mferris/FlightRadar/HANDOFF.md

# FlightRadar — Handoff Notes

## Status
`index.html` is a matured version of `docs/original-prototype.html` that renders
**live** aircraft on the round radar instead of the fake demo data. It has been
tested against the real receiver at `http://192.168.4.77/tar1090/` and confirmed
working: live positions, altitude-coded colors, smooth interpolation between
1s polls, a "NO SIGNAL" banner on connection loss (tested by killing the feed),
and clean recovery on reconnect.

It is now **deployed and running on the Pi** (`[hostname-redacted]`, `192.168.4.77`,
user `mferris`) as a Chromium kiosk launched by systemd, verified to survive a
full reboot with no manual intervention.

**Naming note**: the project was renamed FlightWall → FlightRadar -- repo,
app title, bundle ID, deploy service/file names, and the live services
actually running on the Pi are all updated (`flightradar-kiosk.service`,
`flightradar-photo-proxy.service`, `flightradar-approach-store.service`,
`/opt/flightradar/`, lighttpd confs `89`/`91-flightradar-*.conf`). The
approach-track store's accumulated data (4,788 points at migration time)
was preserved across the cutover: fetched via the old service's own GET
`/approaches` before touching anything, POSTed into the new service after
it was up, verified the count matched on both sides before deleting the
old service/files. The **Pi's actual system hostname is still
`[hostname-redacted]`**, and the Tailscale Funnel URL is unchanged too — those are
real infrastructure identifiers, not just branding, and changing them would
mean re-registering Tailscale and likely getting a new Funnel URL (breaking
any existing bookmarks/links). Left alone deliberately; revisit only if
that's ever specifically wanted. (The real hostname itself, along with the
receiver's exact address/coordinates, is intentionally kept out of this
repo -- see the "Security & going public" section below. The iOS app's
`APIConfig.defaultBaseURL` now defaults to the generic `raspberrypi.local`
instead, with your own real hostname set locally in Settings.)

## Display center override
`index.html` has a `HOME_OVERRIDE` constant that, when set, centers the
radar/map/runway lookup on a fixed point instead of the receiver's real
position — deliberately **display-only**, never touching `readsb`'s actual
configured position (`/etc/default/readsb`, `--lat`/`--lon`), which needs to
stay accurate to the real antenna for its own signal-range/MLAT math.

**Currently `null`** — back to auto-detecting the real receiver position
from `receiver.json` (confirmed against the real antenna's configured
`--lat`/`--lon` to within normal geocoding precision). It was briefly set to
a different address for a one-off request, then reverted.

If it's ever set again: `loadHome()` skips fetching `receiver.json` and uses
the override synchronously instead, and `normalizeAircraft()` always
computes bearing/range via haversine from raw lat/lon rather than trusting
readsb's precomputed `r_dst`/`r_dir` — those are relative to the *real*
antenna position, not an override point, and would silently produce a
geometrically-inconsistent display if trusted while overridden. (Verified by
hand while it was active: an aircraft readsb reported `r_dst: 3.77` for
showed up correctly as `14.53` in FlightRadar — its true haversine range from
the override point.) Also worth knowing: a override point far from the real
antenna shifts the visible 40nm disc so it only partially overlaps the
antenna's actual reception area.

## Remote access (Tailscale Funnel)
The page is also reachable from outside the local network via Tailscale
Funnel, at the same real hostname noted above (kept out of this repo) —
publicly
reachable HTTPS, no login/app required for whoever you send the link to, no
router port-forwarding involved. `tailscale` is installed on the Pi, signed
into `mferris`'s tailnet, with `tailscale funnel --bg 80` proxying that
public URL to lighttpd on `127.0.0.1:80` (the same server `index.html` and
`/tar1090/` are already deployed to, so this is the exact same page, not a
separate copy). Funnel exposes the **whole** site, not just `index.html` —
`/tar1090/` itself is also reachable at that URL, fine for this use case
since it's just flight data, but worth remembering before deploying anything
more sensitive to this docroot later.
- Check status: `ssh mferris@192.168.4.77 tailscale funnel status`
- Turn off: `ssh mferris@192.168.4.77 sudo tailscale funnel --https=443 off`
- The Funnel/serve config is stored in tailscaled's persistent state, so it
  should come back automatically on reboot (not yet verified with an actual
  reboot test the way the kiosk service was — worth confirming if this
  matters going forward).

### Hardening done after enabling Funnel
Turning Funnel on prompted a quick look at what else was reachable on the
Pi. Two things worth knowing:
- **readsb's raw/Beast/SBS ports (30001-30005, 30104) are now bound to
  `127.0.0.1` only** (`--net-bind-address 127.0.0.1` added to `NET_OPTIONS`
  in `/etc/default/readsb`, original backed up alongside as
  `readsb.bak`). They used to listen on `0.0.0.0` — reachable from the whole
  LAN — but nothing on the network was actually connected to them, and
  FlightRadar/tar1090 don't use them at all (they read the JSON files readsb
  writes to disk, not these TCP ports). If you ever want to feed a live raw
  feed to another device on your LAN (Virtual Radar Server, a second
  receiver dashboard, etc.), you'll need to revert this
  (`sudo cp /etc/default/readsb.bak /etc/default/readsb && sudo systemctl
  restart readsb`).
- **Deliberately left `mferris`'s passwordless sudo as-is.** Requiring a
  password would block the non-interactive SSH commands this whole project's
  deployment workflow depends on. This is a real trade-off, not an
  oversight — revisit if that workflow ever changes (e.g. moving deploys to
  a proper CI pipeline instead of ad-hoc SSH).
- **Network segmentation (Eero guest network) was suggested but not done**
  — the Pi's on `wlan0` (WiFi, not Ethernet), so Eero's guest network
  feature would apply cleanly, but doing this yourself: it isolates the Pi
  from the rest of the LAN, which also means your other devices lose
  ad-hoc local access to `http://192.168.4.77/` — Tailscale (already set up
  for Funnel) would keep working as the way to reach the Pi afterward,
  network-topology-independent.

The radar also now has a **background map** (MapLibre GL JS, vendored under
`vendor/` — BSD-3-Clause, v5.24.0, self-hosted so the only runtime network
dependency is the tile/style fetch itself). The map is non-interactive
(`interactive: false`), centered on `home`, and zoomed so its visible extent
matches the radar's `RANGE_NM` ring exactly (`zoomForRange()` in
`index.html` derives the zoom level from the standard Web Mercator
meters-per-pixel formula — recomputes correctly if `RANGE_NM` or the
receiver location ever changes, nothing hardcoded). Requires the Pi to have
internet access for tiles (confirmed working); the ADS-B tracking itself has
no such dependency and keeps working if the map layer fails to load (falls
back to the original solid dark background via CSS).

**Style is OpenFreeMap's `liberty`**, not their `dark` style — `dark` turned
out to be near-grayscale by design (checked the actual style JSON: water,
parks, and woods are all defined at ~0% saturation), so no amount of CSS
`saturate()` could pull color out of it. `liberty` has real color (blue
water, green parks, warm orange/yellow road tones) which we darken ourselves
via `#mapbg`'s CSS `filter: brightness(0.3) saturate(1.5)` — tuned live in a
few iterations to land on "still reads as a dark backdrop" without going all
the way back to washed-out or invisible. Since `liberty` is styled for a
light background (place-name labels are black text with a white halo),
`recolorLabels()` flips city/town/village/water-name labels to light
text/dark halo after the style loads, via the same `setPaintProperty`
pattern already used for the runway layer colors — otherwise the labels
would darken along with everything else and become illegible.

The map also shows **real runway outlines** at airports in range (e.g. RDU's
crossing-runway pattern). The OpenFreeMap tileset's own `aeroway-*` layers
turned out to be a dead end — confirmed via `queryRenderedFeatures()` that the
vector tiles simply carry no runway/taxiway geometry below zoom ~11, and our
fixed radar zoom is ~9.7, so raising the style's `minzoom` did nothing (the
data isn't in the tile, not just hidden). Runways instead come from a
one-time query to OSM's public Overpass API (`loadRunways()`, fired once from
`map.on('load', ...)` since the receiver's home location never changes at
runtime), added as our own GeoJSON source/layers — this bypasses the vector
tileset's zoom restriction entirely since a GeoJSON source isn't tile-paginated.
Purely additive: if Overpass is unreachable the map/radar work exactly as
before, just without runway outlines.

Each tracked aircraft now shows a **color-coded airline badge** (full name,
e.g. "Piedmont Airlines" — or "Private Aircraft" for GA/unidentified flights),
a **human-readable aircraft type** (e.g. "Bombardier Regional Jet CRJ-900",
"Bell 429 GlobalRanger"), and its **route** as city names (e.g. "Tampa →
London") when one's known. A few deliberate choices here, worth preserving:
- **No real airline logos.** They're trademarked, and this project is meant
  to be published under MIT — bundling them would ship trademarked assets in
  an openly-redistributable repo. The `AIRLINES` table in `index.html` instead
  has a small hand-picked set of ICAO designators (ICAO Doc 8585, a public
  standard) mapped to a full name/IATA code/loosely-associated color, rendered
  as a generated text badge. Not exhaustive — unmapped carriers just fall
  back to the airline's ICAO code not being in the table (rare); anything
  whose callsign doesn't match the airline-flight-number pattern at all
  (`/^[A-Z]{3}\d/`) gets "Private Aircraft" instead.
- **Route data comes from `https://adsb.im/api/0/routeset`** — the same free,
  no-key API `tar1090` itself already uses on this Pi (confirmed by reading
  `planeObject_*.js`'s `routeDoLookup()` on the box). ADS-B itself carries no
  route info at all. Lookups are batched/cached/throttled in `index.html`
  (`queueRouteLookup`/`flushRouteQueue`) the same way tar1090 does it: one
  POST per `ROUTE_BATCH_MS` (4s), results cached for the rest of the session
  (including negative "no route found" results, so unknown callsigns aren't
  re-queried every cycle). Routes the API itself flags `plausible: false` are
  treated as unknown rather than displayed (tar1090 doesn't bother with this
  check, but showing a route the API itself doubts felt worse than omitting
  it). Displays city names (`_airports[].location`) rather than IATA codes.
- **Aircraft type also has no field in `aircraft.json`** — readsb doesn't
  populate `t`/`desc` there. tar1090 solves this the same way it solves
  routes: a local same-origin database, this time already sitting on the Pi
  as a prefix-trie of small JSON shards under `/tar1090/db-<hash>/` (the hash
  changes whenever tar1090's assets rebuild, so `index.html` discovers the
  current folder name at runtime by regexing it out of `/tar1090/index.html`
  rather than hardcoding it — see `discoverDatabaseFolder()`). `lookupType()`
  walks that trie itself (own implementation, not copied — tar1090's own code
  license is unclear ["Other"/NOASSERTION on GitHub], so this reads the same
  public same-origin data files but isn't a port of their `dbloader.js`).
  Falls back to `icao_aircraft_types2.js` (ICAO type-code -> description) when
  a specific tail's entry has no `typeLong` of its own. `humanizeType()` just
  re-cases ALL-CAPS manufacturer names ("CIRRUS SR-22" -> "Cirrus SR-22")
  without touching model numbers.

**Labels live in a ring around the edge of the dial**, not floating next to
their plane — each label's natural position is its own bearing angle
(`LABEL_RING_RADIUS = R + 60`), eased there via `LABEL_SPRING_TAU` as the
plane moves, and a color-matched SVG leader line (`#leaders`) always
connects the label back to its actual plane position (attached to whichever
edge of the box faces the plane, via `closestPointOnRect()`). Overlap
resolution (`LABEL_SEPARATION_PASSES` iterations) only ever adjusts a
label's *angle* along the ring, never pulls it off — and always resolves
bearing-adjacent neighbors in bearing-sorted cyclic order. That order
preservation is what guarantees leader lines never cross (a standard
property: connecting points on an inner circle to points on an outer ring
in the same cyclic order can't produce crossing chords), not just an
approximation of "minimized." `R` was shrunk from `0.44*W` to `0.38*W` to
free up a real outer band for the ring to live in. One known rough edge:
a label very close to due-north bearing can lightly touch the HUD text at
the top of the stage — rare, and it's a HUD/label interaction rather than
label-on-label overlap, but not yet fixed. This replaced an earlier
version that eased each label toward a fixed offset next to its plane with
plain 2D AABB separation — that avoided label-on-label overlap fine but had
no concept of leader-line crossings at all.

Covers milestones 3–6 and part of 7 from `docs/project-spec.md` — **the round
panel is physically connected now** (HDMI + USB-C touch + its own 5V power via
a USB-C PD charger, confirmed working: `xrandr` shows `HDMI-A-1 connected
1080x1080`, touch enumerates as `Waveshare Waveshare-079-HD` at USB ID
`0712:000a`), and milestone 5 (tap detail panel) is done too. Backlight
brightness has a physical button on the driver board (per Waveshare's docs,
it also supports "HID software dimming" but no public documentation of that
protocol was findable — button is the practical path for now). Not done:
physically mounting the finished enclosure (that's fabrication, not
software).

## Touch interaction (milestone 5)
Tap a plane's blip or label → detail panel (registration, heading, vertical
rate, squawk, precise range/bearing, and now a real photo — see below). Tap
empty space → cycles three display modes (full / map off / map+labels off)
with a toast confirming the mode. Hit-testing is manual coordinate math on
one delegated `pointerup` listener on `.stage`, not per-element
`pointer-events` (the tag divs are `pointer-events:none` by design, and
label positions move every frame anyway). See `findPlaneAtStagePoint()` —
worth knowing: it returns the *first* match in `planes` iteration order, not
the *nearest*, so two blips/labels overlapping within the ~22px hit radius
could occasionally resolve to the "wrong" one of the two. Not fixed, low
stakes (tapping again elsewhere and retrying works fine).

**Aircraft photo**: `deploy/photo-proxy.py` is a small local-only (127.0.0.1)
Python service on the Pi, proxying planespotters.net's photo API — their API
requires a descriptive custom `User-Agent` naming the app, which browser
`fetch()` can never set itself (browsers own that header exclusively), so
this has to happen server-side. `deploy/89-flightradar-photo-proxy.conf`
(lighttpd, `mod_proxy`) routes `/photo/<hex>` to it so the browser's fetch
stays same-origin. Runs as `flightradar-photo-proxy.service`
(`DynamicUser=yes`, no privileges needed), in-memory cache per hex, 24h TTL.
Attribution (required by planespotters.net's terms — photographer credit +
naming the source) is shown as **plain non-clickable text**, not a real
`<a>` link — deliberate, since this same `index.html` also runs unattended
in the kiosk's own Chromium, and risking a tap navigating the kiosk away
from the app with no way back wasn't acceptable, even though a real link
would be fine in a normal browser tab (e.g. via the Funnel URL). Gracefully
shows nothing if planespotters has no photo for that airframe.

## Key facts learned this session
- Receiver home location comes from `http://192.168.4.77/tar1090/data/receiver.json`
  (`lat`/`lon`) — the app fetches this itself at startup rather than hardcoding it.
  Currently somewhere in the Raleigh-Durham area (exact coordinates intentionally
  not recorded here — see "Security & going public" below).
- `aircraft.json` entries already include `r_dst` (range, nm) and `r_dir` (bearing,
  deg) precomputed by readsb relative to the receiver — `index.html` uses these
  directly and only falls back to a haversine calc from raw `lat`/`lon` if they're
  ever missing.
- The Pi's web server (lighttpd) does **not** send CORS headers, so `index.html`
  must be deployed same-origin (i.e. copied onto the Pi itself, served from the
  same host as `/tar1090/`) — it uses relative fetch paths (`/tar1090/data/...`)
  for exactly this reason.
- SSH login is `mferris@192.168.4.77` (not `pi` — that user doesn't exist on this
  image). Passwordless sudo is configured for `mferris`.
- The Pi runs full Raspberry Pi OS (Debian 13 "trixie") with a Wayland desktop
  (`labwc` compositor, `rpd-labwc` session), lightdm with autologin already
  configured for `mferris`. Not a Lite/headless image.
- The round display was **not physically connected** during this session (both
  HDMI ports read `disconnected` via `/sys/class/drm/*/status`) — the compositor
  falls back to a virtual/no-op 1920x1080 output. Everything was verified via
  `grim` screenshots of that virtual output; the app has not yet been visually
  confirmed on the real 1080x1080 round panel.

## Deployment (milestone 6 — done)
- `index.html` lives at `/var/www/html/index.html` on the Pi (root-owned,
  lighttpd's docroot), served at `http://localhost/` — same-origin with
  `/tar1090/`, satisfying the CORS constraint above.
- Kiosk launcher is a **systemd user service**, checked into this repo at
  `deploy/flightradar-kiosk.service` and deployed to
  `~/.config/systemd/user/flightradar-kiosk.service` on the Pi (as `mferris`).
  - Launches `chromium --kiosk ... http://localhost/index.html`
  - `ExecStartPre` waits (up to 60s) for a `wayland-*` socket in
    `$XDG_RUNTIME_DIR` before starting Chromium — needed because the compositor
    isn't up yet at the instant lightdm opens the session. **Important:** don't
    wait on the `$WAYLAND_DISPLAY` env var itself (e.g.
    `-S "$XDG_RUNTIME_DIR/$WAYLAND_DISPLAY"`) — that variable is imported into
    the systemd user manager *after* labwc starts, so a process forked right at
    session-open captures it empty and waits forever. Glob for `wayland-*[0-9]`
    instead.
  - `Restart=always`, `RestartSec=5` for crash recovery.
  - Enabled via `systemctl --user enable` (symlinked into
    `default.target.wants`), plus `sudo loginctl enable-linger mferris` so the
    user's systemd instance starts at boot even before an interactive login
    completes.
- Verified with an actual `sudo reboot`: service came up ~30s after boot with
  zero restarts, no manual login needed, and was rendering live traffic.
- To redeploy `index.html` after future edits:
  `scp index.html mferris@192.168.4.77:/tmp/ && ssh mferris@192.168.4.77 'sudo cp /tmp/index.html /var/www/html/index.html && rm /tmp/index.html'`
  (Chromium will pick it up on next reload/kiosk restart — no service restart
  needed unless the launch flags/URL change.)

## Approach-track store moved from localStorage to a shared server-side service
The RDU approach-track heatmap (below) originally persisted to
`localStorage` — turns out that's scoped per-browser/per-device, so the
kiosk's own accumulated picture was never visible to anyone checking the
page from a separate browser (laptop, phone, the Funnel URL) — each one
just sees its own empty history. Moved to a small same-origin service
instead, same shape as `deploy/photo-proxy.py`:

- **`deploy/approach-store.py`** — a tiny stdlib-only HTTP server on
  `127.0.0.1:8082`. `GET /approaches` returns the accumulated points (JSON
  array of `[lon, lat]`); `POST /approaches` appends more, capped at
  `MAX_POINTS = 6000` (oldest evicted first — the client-side cap in
  `index.html` is now just a courtesy against pathological cases; the
  server enforces its own copy of the same limit regardless). No auth, no
  dedup — multiple viewers open at once could each independently report
  the same real landing, which just over-represents that landing by a
  point or two, not a correctness problem worth the complexity of fixing.
- **`deploy/91-flightradar-approach-store.conf`** (lighttpd, `mod_proxy`)
  routes `/approaches` to it, keeping the browser's `fetch()` same-origin —
  same pattern as `89-flightradar-photo-proxy.conf`.
- **`deploy/flightradar-approach-store.service`** — `DynamicUser=yes`,
  `NoNewPrivileges=yes`, matching `flightradar-photo-proxy.service`, plus
  `StateDirectory=flightradar-approaches` so `approaches.json` survives
  restarts/reboots despite the dynamic user (systemd creates/owns
  `/var/lib/flightradar-approaches` and hands the path to the service via
  `$STATE_DIRECTORY`).
- `index.html`: `loadApproachPoints()` (GET, fired non-blocking at startup
  alongside the type-database discovery) replaces the old synchronous
  `localStorage.getItem` read; `commitApproachTrack()` now updates the
  local in-memory view immediately (so *this* session's map stays
  responsive) and separately fire-and-forgets a POST so the commit is
  shared with everyone else, current and future.

Verified the whole chain locally: GET/POST/cap/eviction behavior on the
service directly, persistence across a service restart, and — the actual
point of this change — that a second, completely independent browser tab
loading the page sees the exact points a first tab had just committed,
proving the "shared across viewers" behavior actually works and isn't just
each browser talking to itself. Deployed and confirmed no regression to the
sibling `tar1090`/`photo-proxy` endpoints already served through lighttpd.

## RDU approach-path visualization (two complementary pieces)
Requested: faint outlines of RDU's approach paths. No good free dataset of
*real* approach procedures exists (unlike runways, which OSM/Overpass has
real geometry for -- FAA approach plates are PDF charts, not simple line
data), so this ended up as two complementary pieces:

1. **`extendedApproachLines()`** (in `loadRunways()`) -- an immediate,
   free approximation: extends each real runway's own centerline outward
   (`RUNWAY_EXTENSION_NM = 8`, roughly a typical ILS/RNAV final segment
   length) using a new `destinationPoint()` helper (the geodesic inverse of
   `haversineBearingRange()` -- given a start point + bearing + distance,
   find the destination). Real final approaches always align with the
   runway heading for the last several miles regardless of which specific
   procedure guides them there, so this is a reasonable stand-in with zero
   new data dependency. Styled faint/dashed (`line-opacity: 0.22`,
   `line-dasharray`) and added to the map *before* the real runway/taxiway
   layers so the crisp real pavement paints on top of it, not competing.

2. **Real accumulated approach tracks** (`updateApproachTracking()`,
   `confirmApproachOnDrop()`, `commitApproachTrack()`) -- the more
   interesting piece: builds a picture from aircraft *actually observed*
   landing at RDU, growing more defined the more landings it sees.
   Candidate points get buffered per-plane (`pl.approachPoints`) while a
   plane is within `RDU_APPROACH_RADIUS_NM` (12) and below
   `RDU_APPROACH_CEILING_FT` (field elevation + 6000ft) -- deliberately
   loose criteria, since bad data is filtered at *confirmation*, not
   collection. A buffer only gets committed to the persistent store if the
   plane is later confirmed to have actually landed: either it reaches
   `'ground'` status within `RDU_APPROACH_CONFIRM_RADIUS_NM` (2.5nm), or --
   since ADS-B reception commonly drops out right at touchdown, especially
   before a receiving antenna is mast-mounted -- it disappears (coasts out
   past `COAST_TOTAL_MS`) close to the field at low altitude
   (`RDU_APPROACH_CONFIRM_ALT_FT`, field elevation + 1500ft). If instead a
   plane climbs back out or flies away without either signal, its buffer is
   discarded -- overflights and go-arounds don't shape the picture, only
   real landings do. Verified all of this directly (buffered-then-committed,
   buffered-then-discarded-on-go-around, and the signal-loss-near-ground
   path) by driving the functions with synthetic lat/lon/alt sequences.

   Persisted to `localStorage` (`flightwall_rdu_approaches_v1`, capped at
   `APPROACH_MAX_POINTS = 6000`, oldest evicted first) so it keeps building
   across kiosk reboots/reloads, not just within one session -- confirmed
   this survives an actual page reload. Rendered as a MapLibre `heatmap`
   layer (`approaches-heat`), tuned low-intensity/faint on purpose, added
   at `map.on('load', ...)` time alongside `loadRunways`/`recolorLabels`/
   `refreshStorms` -- since it has no network dependency (just reads
   localStorage), it always finishes before `loadRunways`'s Overpass
   round-trip does, so the real runway lines naturally paint on top of it
   without needing explicit layer ordering.

   Starts empty on a fresh install by design -- there's no way to
   backfill history, only real traffic from here forward builds it up.

**Testing note**: hit real trouble getting a clean live screenshot of this
in the sandbox's browser preview this session -- MapLibre's `'load'` event
never fired no matter what (confirmed via a throwaway map instance with a
hardcoded zoom, ruling out anything in our own code; also confirmed
OpenFreeMap's style endpoint itself was reachable and fast). Looked like a
stuck WebGL/rendering-context issue specific to that browser-pane process,
possibly from creating many map instances across today's testing without
disposing them -- survived closing tabs and even a full preview-process
restart, so treat it as a known rough edge of long testing sessions in that
environment, not a real bug. Fell back to verifying via direct function
calls (thorough) and a real `grim` screenshot of the actual kiosk (confirmed
the map/runway rendering pipeline itself is unaffected and healthy).

**Unrelated but important, found while checking the kiosk**: the round
panel's physical HDMI connection was down at the time
(`/sys/class/drm/card1-HDMI-A-1/status: disconnected`, compositor fell back
to its virtual/no-op output, same as before the panel was ever connected)
-- a hardware/cable issue, not caused by this deploy. Worth a physical check
next time someone's at the Pi, especially since the new FlightAware antenna
was recently connected and cables may have been disturbed.

## Stock photo hit rate was much lower than it should've been
Reported as "a lot of planes, especially private ones, can tell me the type
but can't find a stock picture." Two real bugs, both in `lookupStockPhoto()`:

1. Was using `action=opensearch`, which only **prefix**-matches Wikipedia
   page *titles* — a much narrower match than it looks like at a glance.
   `typeLabel` strings like "Bombardier Regional Jet CRJ-900" don't share a
   leading prefix with Wikipedia's actual title ("Bombardier CRJ"), so
   opensearch came back empty even though a perfectly good article and photo
   exist. Switched to `action=query&list=search` (real full-text search over
   article content, word order doesn't matter) — confirmed via a real
   browser `fetch()`, not `curl` (see below for why that distinction
   mattered), that this resolves cases opensearch couldn't.
2. **The bigger one**: any failed lookup — including a purely transient one,
   like a momentary network hiccup or rate-limit — was being cached as a
   permanent `null`. Once a given aircraft *type* failed once, it would
   never show a photo again for the rest of the session, no matter how many
   different tails of that type got tapped afterward. This is the exact same
   failure shape `loadRunways()` had before its retry fix, just showing up
   as "this type never gets a photo" instead of "runways never load."
   Fixed by only caching *successful* lookups — a failed one just retries
   next time that type's panel is opened, which is cheap and naturally
   bounded by tap frequency (same tradeoff the specific-tail planespotters
   photo lookup already makes: it isn't cached at all, and re-fetches every
   single time a panel opens).

Worth knowing for next time: while testing, `curl`-hammering Wikipedia's API
rapidly with no descriptive User-Agent tripped an actual 429 ("Please set a
proper user-agent and respect our robot policy") from their edge cache.
That's a `curl`-testing artifact, not something the real app should hit —
browser `fetch()` always sends a real browser UA, and lookups only ever fire
on a human tap, nowhere near hammering pace — but it's worth remembering if
Wikipedia lookups ever look flaky again: check whether it's a real app-level
issue before assuming it's the app doing something wrong, since aggressive
manual testing against the same API can produce misleading transient
failures that don't reflect real usage.

## Runways silently disappearing for a whole session (found this session)
Reported as "I can no longer see the RDU runways." Root cause turned out to
be unrelated to the map alignment fix above — a real, separate,
pre-existing gap: `loadRunways()` only ever ran **once**, on the map's
`load` event, with no retry. A single transient failure from Overpass
(rate-limited, timed out, etc.) at exactly the wrong moment — like right as
the kiosk boots — silently and *permanently* lost runways for that entire
session, since nothing else ever re-triggered the fetch and the kiosk can
run for days before its next reload. Confirmed by hand: called
`loadRunways()` directly a few times back-to-back while testing (which
itself hammers the same shared public Overpass instance) and watched it
return with zero features/an error a couple of times before a retry
succeeded with real data — the exact failure mode, reproduced live. Likely
tripped for real this session specifically because the kiosk got restarted
six separate times deploying today's other changes, each one a fresh
chance to hit it.

Fixed with a bounded retry: up to `OVERPASS_MAX_ATTEMPTS` (4) tries, 20s
apart (`OVERPASS_RETRY_MS`) — generous backoff since this is a shared public
API and only needs to eventually land once per (rare) kiosk reload, not be
fast. Still purely additive/best-effort after retries are exhausted, same as
before — the map/radar work fine without runway outlines either way.

## Trails made always-on for every plane, not just tap-to-show
Preference change: flight trails (see below) now draw for every in-range
aircraft every frame (`drawTrails()`), not just the one with an open detail
panel. The trail *data* was already being collected for every plane
regardless of selection (that was deliberate from the start, so reopening a
panel would show continuity) — only the drawing itself was gated.

Also shortened `TRAIL_MAX_MS` from 10 minutes to 3. That was sized for "one
plane, deep history, only while you're looking at it" — rendering it for
every plane simultaneously, permanently (not just while a panel happens to
be open), is a meaningfully bigger continuous per-frame cost on a Pi running
this render loop 24/7 (up to ~600 line segments per aircraft at the old
window, times however many are in view at once), and a 10-minute trail per
plane all at once is also visually noisy. 3 minutes still clearly shows an
approach/departure into RDU. Worth revisiting (either direction) once seen
running for a while on the real hardware.

## Stock photo fallback for tails with no planespotters photo
Most tracked tails (private/GA especially) have no dedicated planespotters
photo — noticed by actually clicking around on GA traffic. Rather than
always falling back to the generic silhouette, `tryStockPhoto()` now tries a
representative photo of the aircraft *type* instead (any Cessna 172, not
necessarily this exact tail), via Wikipedia/Wikimedia Commons — same
free/no-key-required class of source as adsb.im's routes, RainViewer's
radar, and Overpass's runways elsewhere in this file. `lookupStockPhoto()`
does an `opensearch` query against the plane's `typeLabel` (the same
human-readable type string already shown elsewhere in the UI) to find a
matching Wikipedia page, then the REST `page/summary` endpoint for its
thumbnail — cached per type string (not per hex), so one lookup covers every
Cessna 172 this receiver ever sees. Confirmed CORS actually works for a real
browser `fetch()` against Wikipedia's endpoints (curl doesn't enforce CORS,
so that alone wouldn't have proven it) before relying on it.

Hit rate is decent but not perfect — simple GA types (Cessna/Cirrus/Piper/
Beechcraft) matched cleanly in testing, but regional jets did not (the
`typeLabel` string reads "Bombardier Regional Jet CRJ-900", while Wikipedia's
actual page title is "Bombardier CRJ900" — no fuzzy retry was built for this,
since even an imperfect hit rate is a strict improvement over the previous
always-silhouette fallback, and a failed lookup just falls through to the
same placeholder as before). Deliberately labeled with a visible **"REPRESENTATIVE
PHOTO"** badge overlaid on the image itself (not just smaller credit text)
so it's never mistaken for a real photo of that specific airframe — this is
a real photo of *some* example of that type, not the tracked tail. Credit
line is "site name only" (matching the planespotters credit's existing
non-clickable-text, kiosk-navigation-safety treatment above), a deliberately
lighter touch than full Commons per-image author/license boilerplate would
be — proportionate to what the rest of this app already does, not a new
legal risk tier.

## Map/radar alignment bug (found via the trail feature)
Trying out the new trail near RDU surfaced a real bug: the background map's
zoom was miscalibrated, so real ground features (like RDU's runways) rendered
increasingly far from where the radar independently plots aircraft at the
same true bearing/range, the farther from `home` you looked — accurate right
at the center, visibly "shifted" a few nm out. Two compounding causes in
`zoomForRange()`/`initMap()`:
1. The 156543.03392 constant is meters-per-pixel-at-zoom-0 for the classic
   256px slippy-tile convention, but MapLibre/Mapbox GL define zoom for 512px
   tiles (whole world = 512px at zoom 0) — a well-known porting gotcha
   ("Mapbox GL zoom = Leaflet zoom - 1" for the same visual scale). Using the
   256px constant unmodified renders one zoom level too far in, a *scale*
   error (not a fixed offset), so it's small near `home` and grows with
   distance. Fixed by subtracting 1 from the computed zoom.
2. `zoomForRange` was fed `R`, the radar's radius in the canvas's fixed
   1080-unit *internal* space — but MapLibre's zoom is calibrated against the
   container's actual rendered *CSS* pixel size, which only equals 1080 when
   the stage happens to render at exactly 1080px. True on the physical
   1080x1080 kiosk panel (masking this entirely there, which is why it went
   unnoticed until now), but not for anyone viewing the same page at a
   different size via the Funnel URL. `initMap()` now converts `R` to real
   CSS pixels (`R * stage.getBoundingClientRect().width / W`) before calling
   `zoomForRange()`.
Verified by comparing MapLibre's own `map.project([lon,lat])` for RDU's real
coordinates against the radar's independently-computed `polarToXY()` position
for the same point (via `haversineBearingRange()`) — before the fix these
diverged by a factor tied directly to the test viewport's CSS-vs-canvas
pixel ratio (proving cause #2), after fixing both, they match to ~0.1-0.15%
(the tiny residual being genuine, unavoidable Mercator scale variation across
the visible disc, not a bug). Not yet reconciled: zoom is calibrated once at
`initMap()` time and never recalculated, so a browser window resized *after*
load (e.g. via Funnel, on a desktop) would need a reload to stay aligned —
fine for the kiosk itself (fixed physical resolution, never resized), not
yet handled for the general case.

## Per-type aircraft icons + tap-to-show flight path trail
Prompted by looking at tar1090's own map (`http://192.168.4.77/tar1090/`), which
draws distinct shapes for large commercial jets/smaller jets/prop planes and
shows a flight-path trail when you tap a plane.

**Icons**: didn't port tar1090's actual icon set (`markers.js` on the Pi at
`/usr/local/share/tar1090/git/html/markers.js`, ~100+ hand-drawn SVG paths) —
its code license is unclear ("Other"/NOASSERTION on GitHub, same concern
already noted above for the aircraft-type database), and importing ~100
detailed bezier paths would also be needlessly heavy for a canvas redrawn
every frame on a Pi. Instead, `classifyAircraft()` buckets each plane into
`heavy` / `jet` / `prop` / `heli` / `lta` / `unknown` and `drawBlipShape()`
draws a small hand-coded canvas path for each — same kite/arrowhead as always
for `jet`/`unknown` (no visual change for most traffic), just bigger for
`heavy`, a distinct cross/plus silhouette for `prop`, a rotor-ring-plus-tail
for `heli`, an ellipse for `lta`. Classification prefers the specific tail's
ICAO type info when known (`typeDesc`/`wtc`, from the same
`icao_aircraft_types2.js` database `lookupType()` already reads for the
aircraft-type-string feature above — just two more fields off the same
entries, `[typeLong, typeDescription, wtc]`), falling back to the raw ADS-B
`category` field readsb reports per-aircraft (A1 light .. A5 heavy, A7
rotorcraft, B2 lighter-than-air) when type info isn't known yet or at all —
common for GA tails with no database entry.

**Trail**: tar1090's tap-to-show trail comes from readsb's own trace history
(`data/traces/<hex-suffix>/trace_recent_<hex>.json`), but **this Pi's readsb
doesn't have that enabled** — confirmed via `curl` (404) and `find` (no
`trace_*.json` files anywhere on disk). So the trail is built client-side
instead: each poll's already-computed bearing/range (the same values the live
blip uses) gets pushed onto that plane's `p.trail` array in `applyUpdate()`,
pruned to the last 10 minutes (`TRAIL_MAX_MS`). `drawSelectedTrail()` draws it
as a fading polyline, only while the detail panel is open for that plane.
Real limitation, not a bug: **this only covers time since the page was last
loaded** — there's no real flight history before that, unlike tar1090's
server-backed trail. Worth reconsidering if trace storage is ever enabled on
this receiver.

**Bug fix along the way**: `p.bearing` (the smoothed/eased live bearing used
for blip position) was never wrapped back into `[0, 360)` after each frame's
`+= bearingDelta(...)` — harmless for the actual blip *position* since
`Math.cos`/`Math.sin` are periodic, but the detail panel's `Range/Brg` display
could show something like "482°" for a contact that's been tracked long
enough to accumulate past a full revolution (e.g. a tight holding pattern
near the receiver). Found via testing with a synthetic aircraft deliberately
orbiting fast to exercise the new trail code — real traffic would hit this
rarely, but it's a real latent bug. Fixed by wrapping `p.bearing` the same
way `p.labelAngle` already was two lines below it.

**Testing note**: this sandbox's browser preview can reach the public
internet but not the Pi's private LAN address (192.168.4.77) — `dev-server.py`'s
proxy got `No route to host` even though direct `curl`/`ssh` from a shell
in the same session worked fine. Verified instead with a small mock server
(`/tar1090/data/*` stubbed with synthetic aircraft spanning every category)
so all five shapes and the trail could actually be checked visually and via
canvas pixel sampling, rather than waiting for real traffic to happen to
include a helicopter or blimp. Deployed and confirmed byte-identical on the
Pi, but not yet visually confirmed against live traffic in a real browser —
worth a look next time the kiosk/Funnel URL is checked.

## Open — not yet done
- **Milestone 5** (optional): tap-an-aircraft detail panel.
- **Physical verification on the real panel**: the round 1080x1080 display
  needs to actually be connected via HDMI to confirm rendering, sizing, and
  touch input work on real hardware — not yet possible since it isn't wired up
  in the enclosure yet.

## Dev-only files
`dev-server.py` is a local-only static file server + reverse proxy
(`/tar1090/*` → `192.168.4.77`) used purely to test `index.html` with the same
relative paths it'll use in production, without hitting CORS on a dev machine.
It is **not** part of the deployed app — don't copy it to the Pi. Run it with
`python3 dev-server.py` and open `http://localhost:8000/index.html`.

## Security & going public
Prompted by an explicit ask to review this before making the repo public.
Real findings, all addressed:

- **The Funnel URL leaked exact home coordinates to anyone, unauthenticated**
  — `/tar1090/data/receiver.json` returns survey-precision `lat`/`lon`, and
  Funnel exposes the *whole* site (readsb's own debug UI included), not just
  `index.html`. Fixed with a new local-only filtering proxy,
  **`deploy/funnel-gateway.py`** (`flightradar-funnel-gateway.service`),
  that Funnel is now pointed at instead of lighttpd directly: it rounds
  `receiver.json`'s coordinates to 2 decimal places (~0.7mi) for anyone
  coming in over the public internet, while passing everything else through
  unchanged. LAN access (the kiosk, port 80 directly) still sees the exact
  value — `readsb` itself needs that for its own signal-range/MLAT math,
  unaffected either way.
- **Real address/coordinates/hostname were committed to the repo** (this
  file, `index.html`, the iOS app) — scrubbed from current files and from
  git history (a full-history rewrite + force-push, same approach used
  earlier for the commit-email fix). The iOS app's `APIConfig.defaultBaseURL`
  now defaults to the generic `raspberrypi.local` instead of a real personal
  hostname; set your own in Settings.
- **Stored XSS via third-party content** — `showDetailPanel()` and
  `loadDetailPhoto()` built HTML via unescaped template literals, and the
  photo *photographer credit* comes straight from planespotters.net's own
  user-submitted names. Fixed with an `esc()` helper applied everywhere
  external/semi-trusted data (route text, photographer name, Wikipedia
  image URLs) lands in `innerHTML`.
- **`/approaches` had no auth, no validation, and no body-size cap** —
  reachable from the public internet via Funnel. Anyone could pollute or
  evict the real accumulated approach-track data with a single POST, or
  send an oversized body before any validation ran. Fixed in
  `approach-store.py`: a 200KB cap enforced before the body is even read,
  plus shape/range validation on every point.
  - **A real incident from testing this**: verifying the size cap against
    the *live* endpoint (should have used a non-production target) sent a
    batch that was accidentally under the cap, got accepted as 20,000
    valid-shaped junk points, and evicted the entire real accumulated
    dataset via the existing `MAX_POINTS` eviction. Recovered from a
    leftover, never-cleaned-up state file from the FlightWall→FlightRadar
    migration (`/var/lib/private/flightwall-approaches/`) that still had
    the 4,788-point snapshot from that migration — real data, zero junk,
    restored. Anything accumulated between the migration and this incident
    (roughly 150-200 points) is permanently gone. Worth remembering: don't
    verify destructive-shaped tests against production state, even when the
    code path is "just validation."

**Not yet done / your call**: `dev-server.py`'s hardcoded LAN IP and the SSH
username throughout this file are low-risk (private RFC1918 address, common
username already tied to the public GitHub handle) and weren't in scope of
what was scrubbed above — revisit if that changes. Passwordless sudo on the
Pi remains a deliberate, previously-accepted tradeoff for the SSH-based
deploy workflow, unrelated to whether the repo itself is public.

## Registered-owner lookup for confirmed-private aircraft
For aircraft already classified "Private Aircraft" (a real callsign, just not
one matching an airline's flight-number pattern — see the airline-badge
section above), the detail panel now shows who the airframe is registered
to. Source is `adsbdb.com`'s free, no-key `/v0/aircraft/{hex}` endpoint —
same "free and keyless" bar as every other data source this project uses.
`lookupOwner()` caches only *definitive* answers (a real registrant name
came back); a miss or transient failure isn't cached, same reasoning as the
stock-photo-type cache fix above — a transient failure shouldn't become a
permanent "no owner" for that tail. `loadOwner(hex)` is staleness-guarded so
a slow response for a plane the user has since tapped away from doesn't
clobber whatever's currently showing.

**Explicitly out of scope, asked directly and declined**: going further and
trying to identify the actual person/location behind an LLC-registered
owner. Most private aircraft are registered to a trust or LLC specifically
*because* the FAA offers this as a privacy option (the same reasoning behind
the FAA's LADD "block from public tracking" program) — building
deanonymization on top of that would turn this project into something that
could enable stalking/harassment, especially once it's public and running
against anyone's home address, not just the deploying user's own driveway.
Showing the registrant name/LLC as adsbdb already provides it is the line.

## Sighting counts (total + within-alert-radius)
Every aircraft now tracks how many distinct times this receiver has picked
it up (`total`), and how many of those came within the nearby-alert radius
(`nearby`) — requested specifically to make repeat visits from the same
private aircraft near the house obvious at a glance, not just log them
silently.

Same "shared server-side store, not localStorage" pattern as the
approach-track data (see above) and for the same reason — the kiosk's own
accumulated counts need to be visible to every viewer, not just whichever
browser happens to be open:
- **`deploy/sighting-store.py`** — stdlib-only HTTP server on
  `127.0.0.1:8083`. `GET /sightings` returns the full `{hex: {total,
  nearby}}` map; `POST /sightings` (`{hex, kind}`) increments one counter by
  one and returns the updated pair. Validates the hex format and body size
  up front (`MAX_BODY_BYTES = 2000` — a real body is ~40 bytes, but it's
  reachable from the public internet via Funnel, same caution as
  `approach-store.py` learned the hard way about). `MAX_HEXES = 20000` with
  oldest-inserted-first eviction.
- **`deploy/93-flightradar-sighting-store.conf`** routes `/sightings` to it;
  **`deploy/flightradar-sighting-store.service`** is `DynamicUser=yes` +
  `StateDirectory=flightradar-sightings`, same shape as the photo-proxy and
  approach-store units.
- `index.html`: `recordSighting(hex, kind)` does an optimistic local update
  immediately (so the badge/panel feel instant) and fire-and-forgets a POST,
  reconciled with the server's authoritative response when it lands.
  `'total'` fires the first time `applyUpdate()` creates a plane it hasn't
  seen this session; `'nearby'` fires in `checkNearbyAlert()` the moment
  `pl.alerted` first flips true — **deliberately decoupled from the
  nearby-alert toggle**: counting always happens even while alerts are
  toggled off, only the popup/chime are gated by the toggle.

UI: a "SEEN ×N" badge on the aircraft tag once `total > 1` (hidden at
exactly 1 — a first sighting isn't a repeat, so no badge is the right
default state), plus `Sightings`/`Within 2mi` as always-visible fields in
the detail panel grid.

## Heatmap tuning: "looks good on web, looks like a blob on the kiosk"
Reported after the color change above shipped: the approach-track heatmap
looked distinct and line-like on a laptop browser but rendered as an
undifferentiated blob of color on the physical kiosk. Two rounds:

**First hypothesis (wrong): `devicePixelRatio`.** Tried forcing
`pixelRatio: Math.max(2, window.devicePixelRatio || 1)` on the MapLibre `Map`
constructor, reasoning the kiosk's actual DPR might be producing a
lower-resolution raster of the heatmap layer than a retina laptop screen.
Deployed to the kiosk to test — it made the blob *worse* (bigger, blurrier).
Immediately reverted and redeployed the revert.

**Real root cause: production zoom level, not DPR.** All prior tuning had
been eyeballed against an artificially zoomed-in test view (easy to do by
accident when checking a map interactively), which visually spreads a given
`heatmap-radius` (in pixels) across more geographic area than it actually
covers at the kiosk's real, fixed zoom (`interactive: false`, always at
whatever `zoomForRange()` computes for `RANGE_NM` — see the alignment-bug
section above for how that's derived). At the real production zoom, the
same radius that looked like distinct lines when zoomed in compresses many
genuinely-separate approach tracks into the same handful of pixels — a real
blob, not a rendering artifact. Confirmed by testing with frozen real data
at the true production zoom, on the real styled/darkened map, rather than
an interactively-zoomed view.

Fixed by shrinking `heatmap-radius` (down to `2`) and moving to a brighter,
higher-contrast `heatmap-color` ramp (cyan-based,
`rgba(0,255,225,…)` → `rgba(120,255,240,1)` at full density) so individual
tracks stay visually separable at the real production zoom instead of
merging. Lesson for next time this layer needs tuning: always verify against
the actual fixed kiosk zoom, never a zoomed-in interactive view — the two
can look completely different for the same paint properties.

## Runway outlines occasionally missing after a kiosk restart (second occurrence)
Same underlying symptom as the "Runways silently disappearing" bug fixed
earlier (retry added, see above) still showed up occasionally after a kiosk
restart, even with the retry in place — the retry helps a *transient*
Overpass failure, but does nothing for the ~80-second window during which
none of the `OVERPASS_MAX_ATTEMPTS` retries have completed yet, during which
the map has no runway layer at all.

Added a genuine additional layer of durability: on a successful
`loadRunways()` fetch, the resulting GeoJSON is now also cached to
`localStorage` (`flightradar_runways_v1`). `loadCachedRunways()` reads it
synchronously on `map.on('load', ...)` (registered *before* `loadRunways`
itself in the listener order) via a new `applyRunwayData(geojson)` helper —
factored out so both the cache-read path and the live-fetch-success path
share the same idempotent add-or-update-source logic instead of duplicating
it. Net effect: a kiosk that has ever successfully fetched runway data once
shows it immediately on every subsequent restart, with the live Overpass
fetch (and its retries) only needed to pick up changes or serve a genuinely
fresh install — Overpass being flaky no longer means a blank map for a full
session.

Separately investigated and ruled out as the actual cause of the reported
instance: only 2 of an expected 3-4 retry attempts had fired within the
observed window during testing. Traced to Chrome throttling `setTimeout` in
a backgrounded test tab (kept switching tabs while testing) — confirmed by
invoking `loadRunways()` directly in a foregrounded tab, which succeeded
immediately. Not a real production concern (the kiosk is always
single-window/foreground), but the localStorage caching above is a real fix
regardless, independent of whatever caused this particular report.

## Sighting counts double-incrementing on reception dropouts (found and fixed)
Reported as "flights from 30 minutes ago show 5-6 sightings, but I wasn't
actually there that many times." Root cause: a plane briefly dropping off
ADS-B reception (common with this Pi's antenna, especially for close/low
traffic) drops it from the tracked-planes map after just `COAST_TOTAL_MS`
(8s). If the same physical pass resumed reception seconds or minutes later,
`applyUpdate` and `checkNearbyAlert` had no memory it was just there and
recorded a brand-new "visit" each time.

Fixed with a 5-minute cooldown (`SIGHTING_COOLDOWN_MS`, keyed by hex,
tracked independently of the plane object's own lifecycle via
`recordSightingOnce`) so a signal hiccup mid-pass can't inflate the count,
while a plane genuinely returning later still counts again once the
cooldown elapses. The already-inflated counts from before this shipped were
manually reset to zero on the live store (`sighting-store.py`'s
`sightings.json`) at the user's request — deliberate, not automatic, given
the earlier approach-track data-loss incident's lesson about not touching
production state casually.

## Flight trails no longer time-limited
Reported: trails were disappearing well before a plane left the display.
`TRAIL_MAX_MS` (3 minutes) was a fixed wall-clock cutoff, left over from
when trails were shortened for a different reason (drawn for every plane
every frame instead of just the tapped one — see the "always-on" section
above). Replaced with `TRAIL_MAX_POINTS` (7200, a generous safety cap
against unbounded growth for something like a loitering local helicopter,
not a real cutoff for any normal flight) — a trail now persists for as long
as the plane itself stays tracked, dying with the plane object on coast-out
same as before. Older segments fade toward a floor opacity
(`TRAIL_FADE_FLOOR`) instead of vanishing at a hard time boundary, so the
whole path stays visible while still reading recent-vs-older.

## Emergency squawk and RDU landing/takeoff sound alerts
Requested: audible alerts for emergency squawks (7500/7600/7700) and for
RDU landings/takeoffs.

- **Emergency squawks** (`checkEmergencySquawk`) — a distinct four-beep
  chime (`playEmergencySound`, more insistent than the nearby-alert chime)
  plus an auto-popped detail panel labeled with the specific emergency
  ("HIJACK — SQUAWK 7500" etc, via a new `alertLabel` param on
  `showDetailPanel`). Gated on `pl.emergencyAlerted` so it fires once per
  emergency, not once a second while still squawking.
- **RDU landing/takeoff** (`checkRduPhaseAlert`) — reuses the same
  RDU-proximity/vertical-rate classification already driving the blip color
  (at the time; see below), so "sounds like a landing" always matched
  "drawn like one." A single quiet tone, pitched down for landing and up for
  takeoff, so the two are distinguishable by ear.

Both introduced a shared `playTones(notes)` helper (each note
`[freq, startOffset, dur, peakGain]`), factored out of what used to be
`playAlertSound`'s own body.

## Settings panel replaces the single blind tap-toggle gesture
Once emergency squawks and the RDU phase chime existed alongside the
original nearby-alert toggle, "tap empty space to blindly flip one setting"
stopped making sense — requested a real settings screen instead.

A new gear-icon button (`#gearBtn`) opens a modal (`#settingsPanel`) with
one row per alert/sound concern: nearby-aircraft alert, emergency squawks,
RDU landing/takeoff chime, RDU ATC audio (see below). Persisted to
`localStorage` (`flightradar_alert_settings_v1`) — a personal display
preference, not shared state, unlike the server-side sighting/approach
stores. Tapping empty space now opens this panel instead of directly
toggling nearby alerts; the panel itself dismisses on any tap outside a row
(reusing the same "any tap while X is open closes it" pattern the detail
panel already used).

Emergency squawks became toggleable here too (previously hardcoded
always-on) — but `pl.emergencyAlerted` is only set once the alert actually
*fires*, so if it's off during an ongoing squawk and gets turned back on,
it still alerts for that emergency rather than silently having "already
happened" while muted.

## RDU ATC audio: link, not embed — and a real LiveATC.net outage along the way
Requested: hear live ATC audio for RDU landings/takeoffs. Researched
LiveATC.net's actual Terms of Use (https://www.liveatc.net/legal/, not just
their FAQ summary) before building anything — several clauses are directly
on point:

- §2.1: the license is for personal non-commercial use *only*.
- §3.4: bars making the service "directly available" via another dedicated
  application, explicitly "for profit or not" — closes the
  "but it's free/open-source" loophole.
- §3.3: bars making the service available over another network "where it
  could be used by others" — directly implicated by this project's own
  public Tailscale Funnel exposure.
- §3.15: requires *consulting LiveATC.net first* before linking directly to
  a raw audio stream.

Conclusion: embedding their raw stream in an `<audio>` element would violate
several of these regardless of this project's open-source/non-commercial
status. Implemented instead as a link: `ensureAtcAudio()` opens LiveATC's
own KRDU player page (`hlisten.php`, their HTML page — not the raw stream
URL, so §3.15's "linking directly to a stream" doesn't apply) via
`window.open()` in a normal browser tab. Ordinary use of their site through
an interactive browser, same as anyone bookmarking it themselves.

**Kiosk safety incident, same day**: the very first live test on the
physical kiosk did exactly what was flagged as a risk beforehand —
`window.open()` inside `--kiosk` Chromium (a single locked-down fullscreen
window, no tab bar) opened LiveATC's page in a way that covered the screen
with no touch-reachable way back to the radar. Recovered by SSHing in and
restarting `flightradar-kiosk.service`. Fixed structurally, not just
avoided: the kiosk now launches with `?kiosk=1` on its URL
(`deploy/flightradar-kiosk.service`), and `index.html` reads that as
`IS_KIOSK` to (a) refuse `ensureAtcAudio()` outright there, (b)
force-correct any stale `atc: true` left in that browser's `localStorage`
from testing, and (c) render that one settings row visibly disabled with a
red explanation instead of a switch that does nothing (or worse). Unaffected
everywhere else — laptop, phone, the Funnel URL.

**Real external outage, found during testing**: after the kiosk fix, ATC
audio still didn't play — stuck on "reconnecting in Ns..." forever.
Reproduced the *identical* symptom directly on LiveATC.net's own page (not
our code): `krdu_twr2` (tower) was offline at their end, while `krdu_app2`
(approach/departure) played immediately when tested side by side. Swapped
the mount param; easy to swap back if tower comes back.

## RDU phase indicator changed from a full recolor to a highlight ring
The original design for "this plane is landing/departing at RDU" fully
recolored the blip and label (red for landing, green for takeoff),
replacing the plane's normal altitude-based color. Reported as not working
well in practice — swapping a plane's whole identity color made it *harder*
to track, not easier, especially since it happened while the eye was
already tracking that plane by its established color.

Replaced with a bright green ring around the blip (`RDU_PHASE_HIGHLIGHT`,
drawn un-rotated in `drawPlanes` after the blip itself) and a matching
outline/glow on the label (`.tag.rdu-phase`), layered on top of the normal
altitude color rather than replacing it. `flightPhaseColor(p)` (which used
to return a color) became `rduPhaseOf(p)` (returns `'landing'`/`'takeoff'`/
`null`), used identically by the phase chime and the new highlight-ring
pass, so sound/visual/highlight can never drift out of sync with each other.

This was originally requested as a way to answer "who's being talked about
on ATC audio right now" — real-time correlation between the audio stream's
*content* and a specific aircraft isn't feasible (FlightRadar has no access
to the audio content at all, since it's a link to LiveATC's own tab, not an
embedded stream we control; and even with access, that needs real speech
recognition tuned for noisy aviation radio phraseology). This highlight is
the practical stand-in: "these are the planes plausibly on frequency right
now," not "this specific plane is the one currently transmitting."

## Gear/settings button visibility and placement (several rounds)
Iterated live against the real kiosk: started at 34px/dim-gray/left:20%,
increased to 46px/teal (`var(--mid)`, matching the app's accent
color)/glowing, then moved progressively closer to the dial's edge per
feedback — left:8% → left:5%, and vertically from an off-center 40% back to
dead-center 50% (due west) per explicit request, despite that being exactly
where a due-west aircraft's own label anchors (`LABEL_RING_RADIUS`) and can
occasionally overlap the button. Accepted tradeoff, same as labels already
sometimes overlap each other during heavy traffic — the button still
renders on top (z-index) and stays tappable either way.
