mferris/FlightRadar/enclosure/Kitten Enclosure Two-Tone/stand_tail_tip.stl

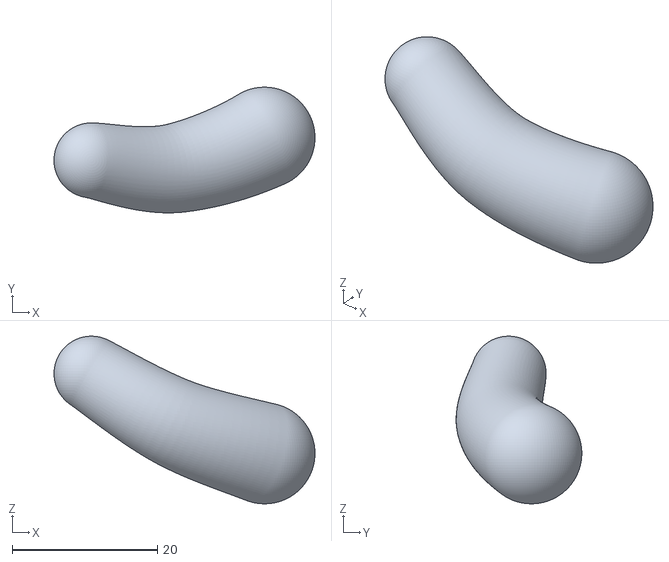
[picture p17: CAD file, 2026-09-06]
enclosure/Kitten Enclosure Two-Tone/stand_tail_tip.stl
35.9 x 17.3 x 23.0
