mferris/FlightRadar/enclosure/Retro Radar Enclosure/retainer.stl

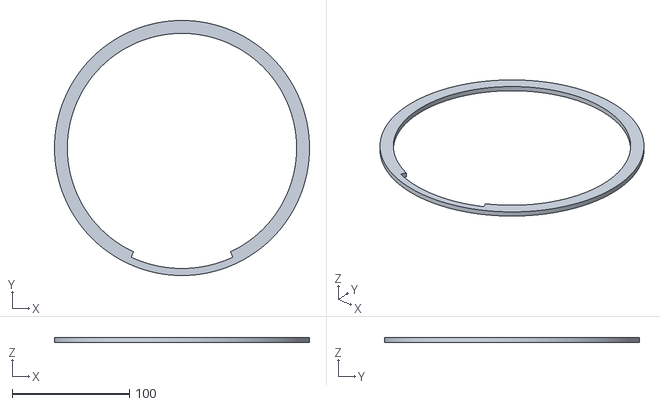
[picture p18: CAD file, 2026-09-05]
enclosure/Retro Radar Enclosure/retainer.stl
217.3 x 217.3 x 4.00
