mferris/FlightRadar/enclosure/Kitten Enclosure Two-Tone/stand_toes.stl

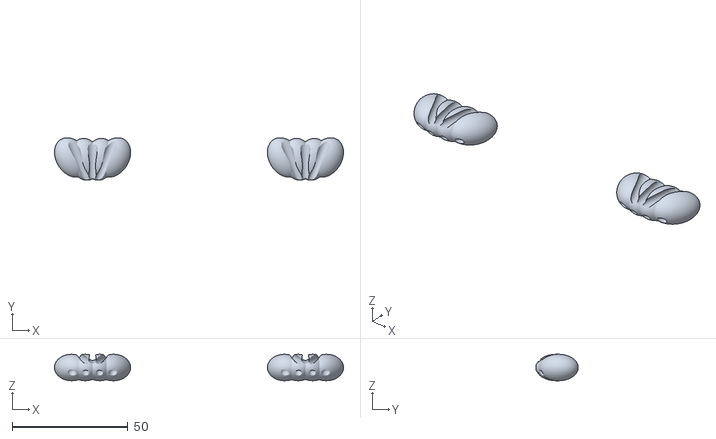
[picture p19: CAD file, 2026-09-06]
enclosure/Kitten Enclosure Two-Tone/stand_toes.stl
124.9 x 18.4 x 11.5
