mferris/FlightRadar/enclosure/Kitten Enclosure Two-Tone/stand_tail.stl

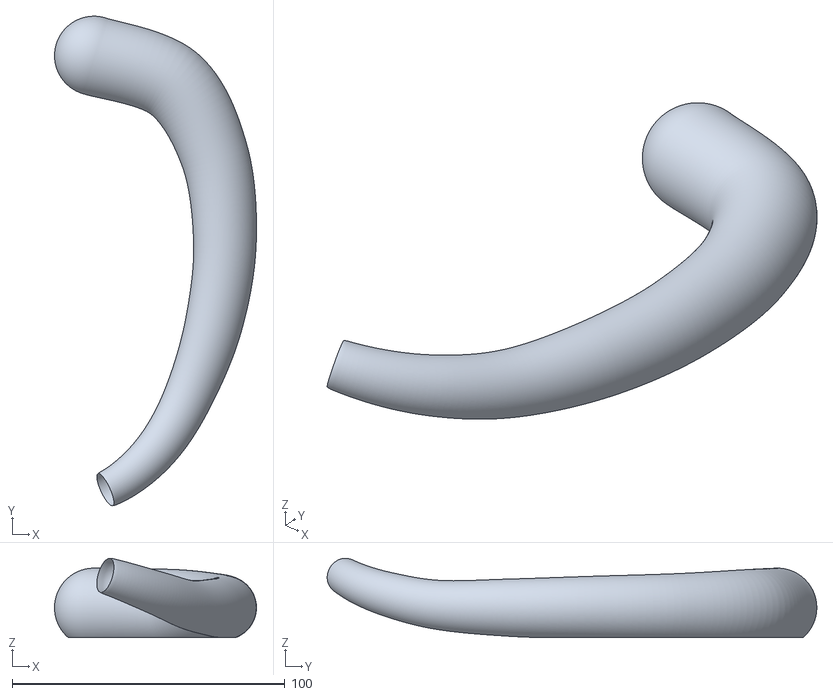
[picture p20: CAD file, 2026-09-06]
enclosure/Kitten Enclosure Two-Tone/stand_tail.stl
74.1 x 179.6 x 29.1
