mferris/FlightRadar/enclosure/Kitten Enclosure Two-Tone/stand.stl

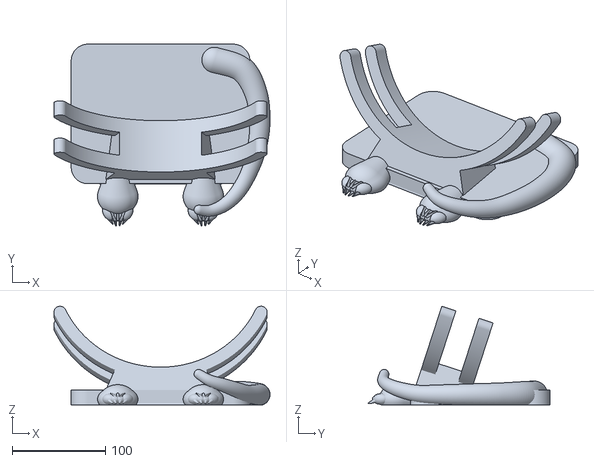
[picture p21: CAD file, 2026-09-06]
enclosure/Kitten Enclosure Two-Tone/stand.stl
232.1 x 195.3 x 105.9
