mferris/FlightRadar/enclosure/Kitten Enclosure Two-Tone/front_trim.stl

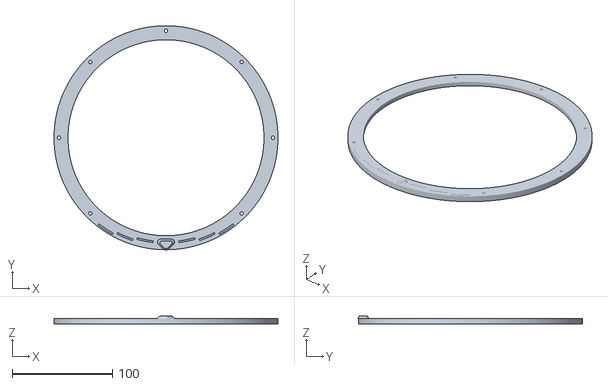
[picture p22: CAD file, 2026-09-05]
enclosure/Kitten Enclosure Two-Tone/front_trim.stl
223.3 x 223.8 x 8.22
