mferris/FlightRadar/deploy/funnel-gateway.py

#!/usr/bin/env python3
"""
Local-only reverse proxy sitting between Tailscale Funnel and lighttpd.

Funnel makes whatever it points at reachable by anyone on the public
internet, unauthenticated -- lighttpd (127.0.0.1:80) also serves the LAN
and the kiosk itself, which both legitimately need exact data (readsb's own
signal-range/MLAT math depends on the real configured position; nothing
about that changes here). This gateway is what Funnel is pointed at instead
of lighttpd directly, so only the copy that actually leaves the house over
the public internet gets filtered -- LAN/kiosk traffic never touches this
process at all.

Every request is proxied through unchanged except one: GET
/tar1090/data/receiver.json (readsb's own receiver-location endpoint, which
index.html's loadHome() fetches to auto-center the radar) has its lat/lon
rounded to 2 decimal places -- about 0.7 miles of fuzz, plenty to keep the
map/radar centered correctly at the app's actual range scale, but no longer
a literal street address to anyone who curls the Funnel URL.
"""
import http.server
import json
import posixpath
import re
import urllib.error
import urllib.parse
import urllib.request

UPSTREAM = "http://127.0.0.1:80"
LISTEN = ("127.0.0.1", 8085)
ROUNDED_PATH = "/tar1090/data/receiver.json"
# readsb puts every aircraft's distance and bearing FROM THE ANTENNA in
# aircraft.json (r_dst, r_dir). With the aircraft's own lat/lon, that locates
# the antenna exactly: measured 2026-09-28 against RDU's public URL, three
# aircraft put it within 54 m, which made rounding receiver.json pointless.
# Public requests get the feed without them; the page falls back to
# computing range from the (rounded) receiver position.
STRIPPED_PATH = "/tar1090/data/aircraft.json"
STRIPPED_FIELDS = ("r_dst", "r_dir")
COORD_PRECISION = 2  # decimal places -- ~0.7mi at this latitude

# Paths refused for public (Funnel) traffic. /wake physically powers the
# kiosk's display on; harmless in isolation, but it is an unauthenticated
# side effect on hardware in someone's house, and nothing off-LAN has any
# business reaching it. The kiosk and the rest of the LAN talk to lighttpd
# directly and are unaffected by this.
# /tts is text-to-speech: CPU-heavy synthesis on the unit, which only the
# house needs; a public caller could otherwise keep the Pi busy talking.
LOCAL_ONLY_PATHS = ("/wake", "/setup", "/tts")

# Paths that may be READ publicly but must not be WRITTEN publicly.
#
# The shared stores accept POSTs with no authentication -- fine when the only
# clients were on the LAN, but the Funnel makes them writable by anyone
# holding the URL. Verified: a POST through the tunnel successfully injected
# a fake sighting. A stranger could pollute the sighting counts and the
# approach heatmap, which is months of accumulated data.
#
# Reads stay open, because the page itself needs them from public viewers.
READ_ONLY_PUBLIC_PATHS = ("/sightings", "/approaches", "/network", "/api")

# A future edit that empties or mistypes this list would silently expose the
# device's privileged endpoints to the public internet. Fail loudly instead.
assert "/wake" in LOCAL_ONLY_PATHS and "/setup" in LOCAL_ONLY_PATHS, \
    "LOCAL_ONLY_PATHS must keep /wake and /setup off the public tunnel"

# How a listed path is matched. This MUST mirror how lighttpd decides which
# backend a request reaches, or the two disagree and the gap is an exposure.
#
# lighttpd routes on a bare regex prefix -- $HTTP["url"] =~ "^/setup" -- so
# /setupx, /setup-ui.html and /wakeup all reach the privileged backends.
# This gateway used to match only the exact path or "<path>/", which is
# strictly narrower. The difference was live and reachable from the public
# internet: /setupx returned the setup server's own 401 (its session auth was
# the only thing left standing), /wakeup reached the wake service, and POST
# /sightingsx and /networkx sailed past the read-only guard into the stores.
#
# Prefix matching is deliberately broader than lighttpd's, not narrower:
# _normalise() casefolds, so /SETUP is refused here even though lighttpd's
# regex is case-sensitive and would not have routed it. Over-refusing on the
# public tunnel costs nothing -- no legitimate public path begins with any of
# these prefixes.
def _matches(base, paths):
    return any(base.startswith(p) for p in paths)


def strip_antenna_relative(data):
    """aircraft.json without the fields measured from the antenna (STRIPPED_FIELDS)."""
    if isinstance(data, dict) and isinstance(data.get("aircraft"), list):
        for a in data["aircraft"]:
            if isinstance(a, dict):
                for k in STRIPPED_FIELDS:
                    a.pop(k, None)
    return data


def forward_headers(items):
    """Headers to send upstream: per-hop ones dropped, the public marker set.

    Split out of _proxy() so the security property is testable without a
    socket -- the marker being set is the whole point, and the previous
    version's failure was precisely that nobody could see it wasn't.
    """
    drop = HOP_BY_HOP | {PUBLIC_MARKER.lower()}
    out = {k: v for k, v in items if k.lower() not in drop}
    out[PUBLIC_MARKER] = "1"
    return out

# Headers that are per-hop or would otherwise be wrong to blindly forward
# (Content-Length is recomputed for the rewritten path; "server" is excluded
# so lighttpd's own version banner doesn't leak through this gateway on top
# of -- see version_string() below -- our own; the rest are transport-level,
# not meaningful to relay from an internal proxy hop).
HOP_BY_HOP = {"connection", "keep-alive", "transfer-encoding", "content-length", "host", "server"}

# Marks a request as having arrived from the public tunnel, so a backend can
# refuse it even if the path filter above has a gap. setup-server.py has
# checked for this header since it was written -- but nothing ever set it, so
# the "belt and braces" it documented did not exist. Demonstrated against the
# live tunnel: /setupx returned 401 (marker absent, request reached the setup
# server) and 404 only when the CLIENT supplied the header itself.
#
# So it is set here, and any client-supplied copy is dropped first: a value
# that a caller can choose is not evidence of anything. Backends may now treat
# its presence as trustworthy.
PUBLIC_MARKER = "X-FR-Public"

# Cheap, zero-risk hardening now that this is reachable from the whole
# public internet: clickjacking/MIME-sniffing/referrer-leak protections.
# Deliberately NOT a Content-Security-Policy here -- this app talks to enough
# different external hosts (map tiles, fonts, several free data APIs) that a
# CSP tight enough to matter needs to be built and tested against the live
# page, not improvised inline; getting it wrong risks breaking the app for
# every public viewer, worse than the marginal defense-in-depth it'd add on
# top of the XSS fix already in index.html.
SECURITY_HEADERS = {
    "X-Frame-Options": "DENY",
    "X-Content-Type-Options": "nosniff",
    "Referrer-Policy": "no-referrer-when-downgrade",
}


class _NoRedirect(urllib.request.HTTPRedirectHandler):
    """Relay redirects to the client instead of following them here.

    urlopen follows 3xx by default, which made this gateway hang: lighttpd's
    captive-portal rule returns a redirect to the hotspot address, and when
    the hotspot is down that address does not exist -- so the gateway sat
    there until timeout with a worker blocked, on a PUBLIC endpoint. Enough
    such requests is a denial of service.

    A proxy has no business chasing redirects anyway: the client should see
    the 3xx and decide.
    """

    def redirect_request(self, req, fp, code, msg, headers, newurl):
        return None


_opener = urllib.request.build_opener(_NoRedirect)


class Handler(http.server.BaseHTTPRequestHandler):
    def version_string(self):
        return "StratoScan"  # don't advertise the Python/http.server version

    def _send_security_headers(self):
        for k, v in SECURITY_HEADERS.items():
            self.send_header(k, v)

    @classmethod
    def _is_read_only_public(cls, path):
        return _matches(cls._normalise(path), READ_ONLY_PUBLIC_PATHS)

    @classmethod
    def _is_rounded_receiver_json(cls, path):
        # Was a bare `path == ROUNDED_PATH` -- a real hole, since self.path
        # includes the query string and isn't traversal-collapsed. GET
        # /tar1090/data/receiver.json?x=1 (or a trailing slash, or any of the
        # percent-encodings _normalise() exists to defeat) failed that exact
        # match and fell through to the unfiltered _proxy(), leaking the
        # real, unrounded home coordinates to anyone with the Funnel URL.
        # Same class of bug as the /wake bypass _normalise()'s own docstring
        # documents; this call site just hadn't been switched over to it.
        return cls._normalise(path) == ROUNDED_PATH

    def _dispatch(self):
        """Single gate for every HTTP method.

        Previously only do_GET and do_POST checked LOCAL_ONLY_PATHS, so any
        method added later would silently bypass it. Deny first, always.
        """
        if self._is_local_only(self.path):
            self.send_error(404)  # 404, not 403 -- don't confirm it exists
            return
        # Public traffic may read the shared stores but never write them.
        if self.command != "GET" and self._is_read_only_public(self.path):
            self.send_error(403, "Read-only")
            return
        if self.command == "GET" and self._is_rounded_receiver_json(self.path):
            self._serve_rounded_receiver_json()
        elif self.command in ("GET", "HEAD") and self._normalise(self.path) == STRIPPED_PATH:
            self._serve_stripped_aircraft_json()
        else:
            self._proxy()

    do_GET = _dispatch
    do_POST = _dispatch
    do_HEAD = _dispatch
    do_PUT = _dispatch
    do_DELETE = _dispatch
    do_PATCH = _dispatch
    do_OPTIONS = _dispatch

    @staticmethod
    def _normalise(path):
        """Reduce a request path to the form the UPSTREAM server will act on.

        Matching the raw path is not enough and was a real hole: lighttpd
        percent-decodes and collapses traversal before routing, so /%77ake,
        /./wake and /x/../wake all reach the wake service while none of them
        string-compare equal to "/wake". Verified against the live gateway --
        all three returned 204 instead of 404.

        Decode repeatedly, because a single pass turns %2577 into %77 rather
        than into "w".
        """
        base = path.split("?", 1)[0].split("#", 1)[0]
        for _ in range(4):
            decoded = urllib.parse.unquote(base)
            if decoded == base:
                break
            base = decoded
        base = base.replace("\\", "/")          # defensive: some clients send backslashes
        base = re.sub(r"/{2,}", "/", base)      # //wake -> /wake
        if not base.startswith("/"):
            base = "/" + base
        base = posixpath.normpath(base)         # /x/../wake -> /wake
        if not base.startswith("/"):            # normpath can yield ".."
            base = "/" + base.lstrip("./")
        return (base.rstrip("/") or "/").casefold()

    @classmethod
    def _is_local_only(cls, path):
        return _matches(cls._normalise(path), LOCAL_ONLY_PATHS)

    def _serve_rounded_receiver_json(self):
        try:
            with _opener.open(UPSTREAM + self.path, timeout=5) as upstream:
                data = json.loads(upstream.read())
        except Exception:
            self.send_response(502)
            self.end_headers()
            return

        for key in ("lat", "lon"):
            if isinstance(data.get(key), (int, float)):
                data[key] = round(data[key], COORD_PRECISION)

        body = json.dumps(data).encode()
        self.send_response(200)
        self.send_header("Content-Type", "application/json")
        self.send_header("Content-Length", str(len(body)))
        self.send_header("Cache-Control", "no-store")
        self._send_security_headers()
        self.end_headers()
        self.wfile.write(body)

    def _serve_stripped_aircraft_json(self):
        try:
            with _opener.open(UPSTREAM + STRIPPED_PATH, timeout=5) as upstream:
                data = json.loads(upstream.read())
        except Exception:
            self.send_response(502)
            self.end_headers()
            return
        body = json.dumps(strip_antenna_relative(data), separators=(",", ":")).encode()
        self.send_response(200)
        self.send_header("Content-Type", "application/json")
        self.send_header("Content-Length", str(len(body)))
        self.send_header("Cache-Control", "no-store")
        self._send_security_headers()
        self.end_headers()
        if self.command == "GET":
            self.wfile.write(body)

    def _proxy(self):
        length = int(self.headers.get("Content-Length", 0) or 0)
        body = self.rfile.read(length) if length else None

        req_headers = forward_headers(self.headers.items())
        req = urllib.request.Request(UPSTREAM + self.path, data=body, headers=req_headers, method=self.command)

        try:
            with _opener.open(req, timeout=10) as upstream:
                self._relay(upstream.status, upstream)
        except urllib.error.HTTPError as e:
            self._relay(e.code, e)
        except Exception:
            self.send_response(502)
            self.end_headers()

    def _relay(self, status, resp):
        self.send_response(status)
        for k, v in resp.getheaders():
            if k.lower() not in HOP_BY_HOP:
                self.send_header(k, v)
        self._send_security_headers()
        self.end_headers()
        self.wfile.write(resp.read())

    def log_message(self, fmt, *args):
        pass  # every request from every public viewer would otherwise hit the journal


if __name__ == "__main__":
    http.server.ThreadingHTTPServer(LISTEN, Handler).serve_forever()
